cholan2100/lna-ai/renders/top_composite_2d.png

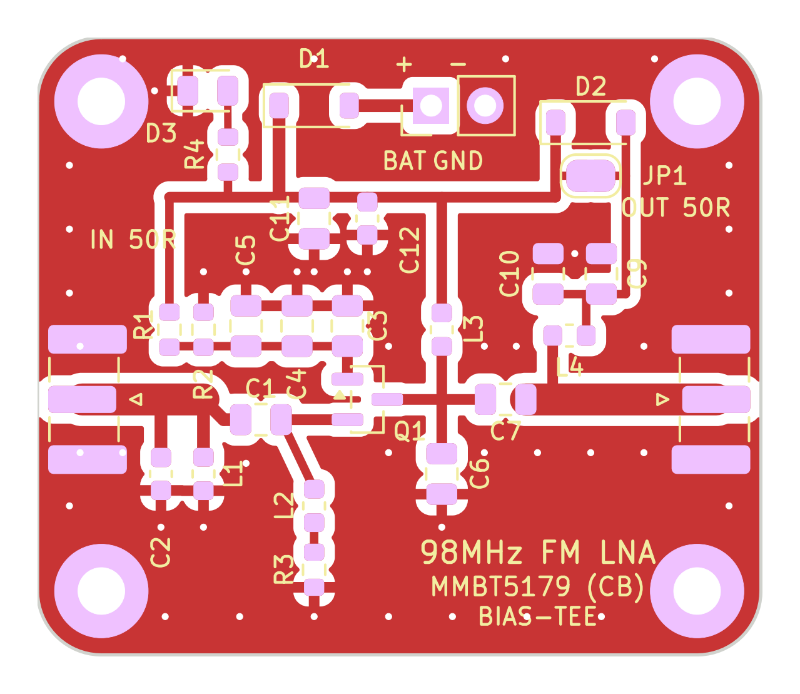
renders/top_composite_2d.png
