cholan2100/lna-ai/renders/top_copper_layer.png

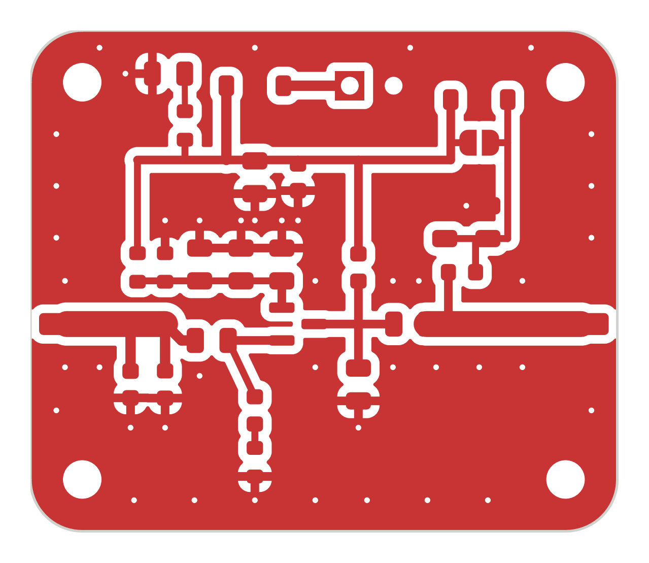
renders/top_copper_layer.png
