cholan2100/lna-ai/renders/top_copper_mask_neg.png

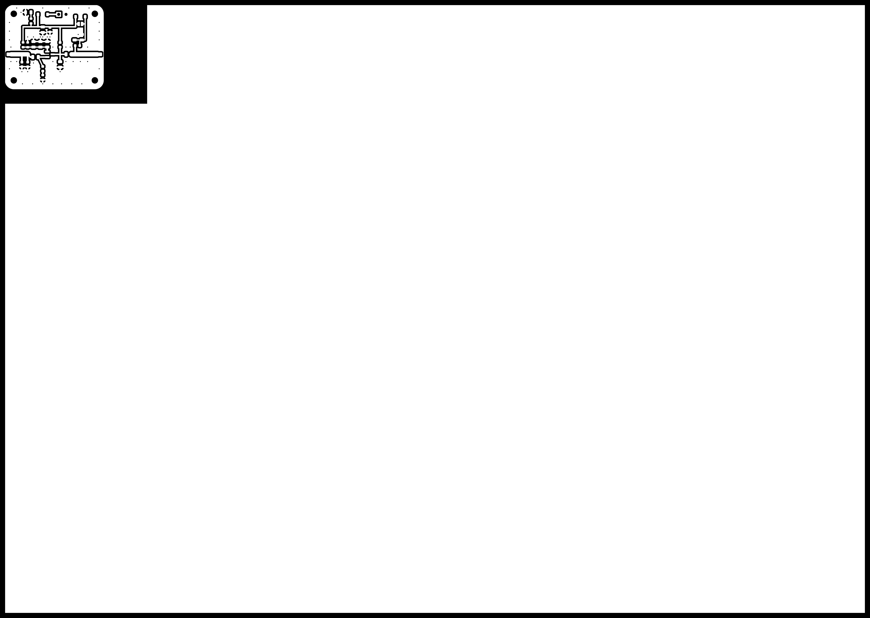
renders/top_copper_mask_neg.png
